HenrykRichter/A500KB/3DPrint/Checkmate_KB_Case/Case_Finished.jpeg

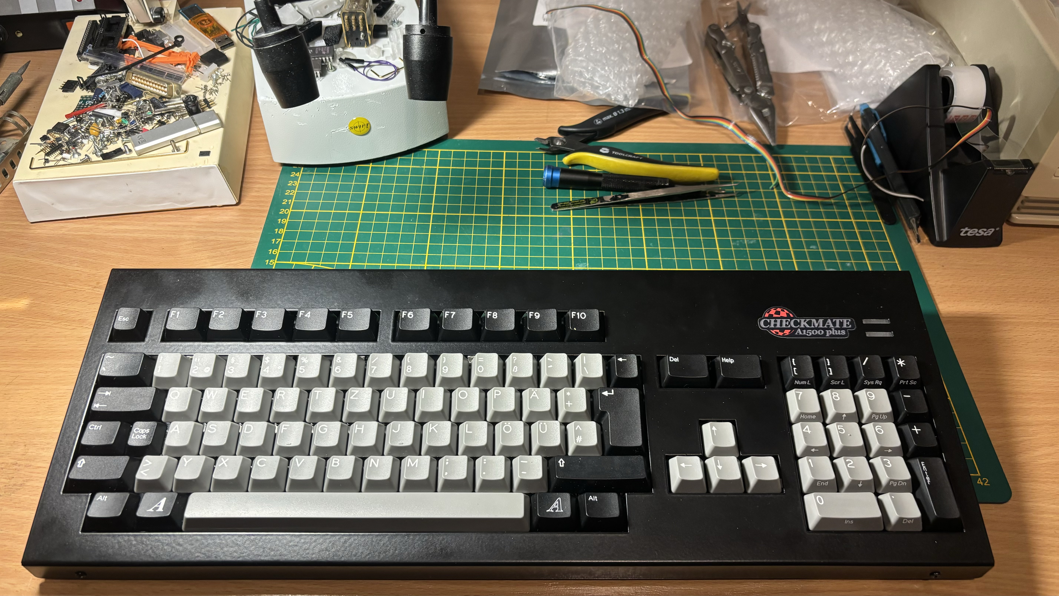
3DPrint/Checkmate_KB_Case/Case_Finished.jpeg
