HenrykRichter/A500KB/3DPrint/Checkmate_KB_Case/Case_Holders_Bottom.jpeg

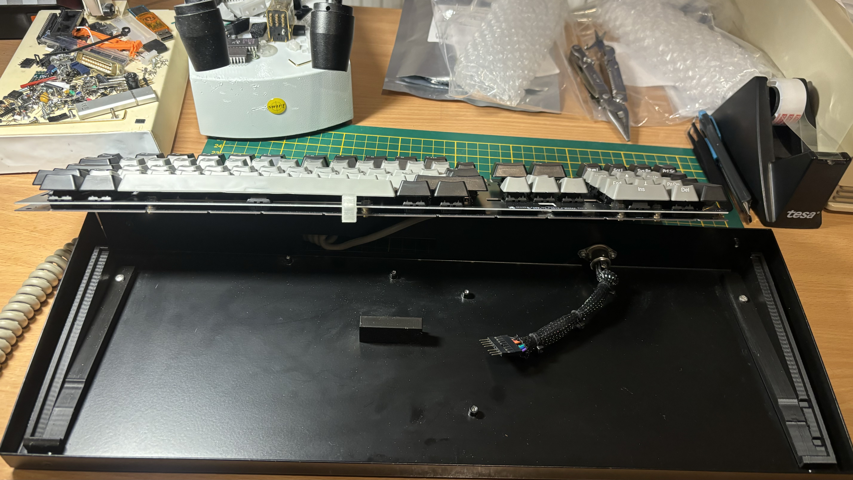
3DPrint/Checkmate_KB_Case/Case_Holders_Bottom.jpeg
