HenrykRichter/A500KB/Pics/A500KB_Config.JPG

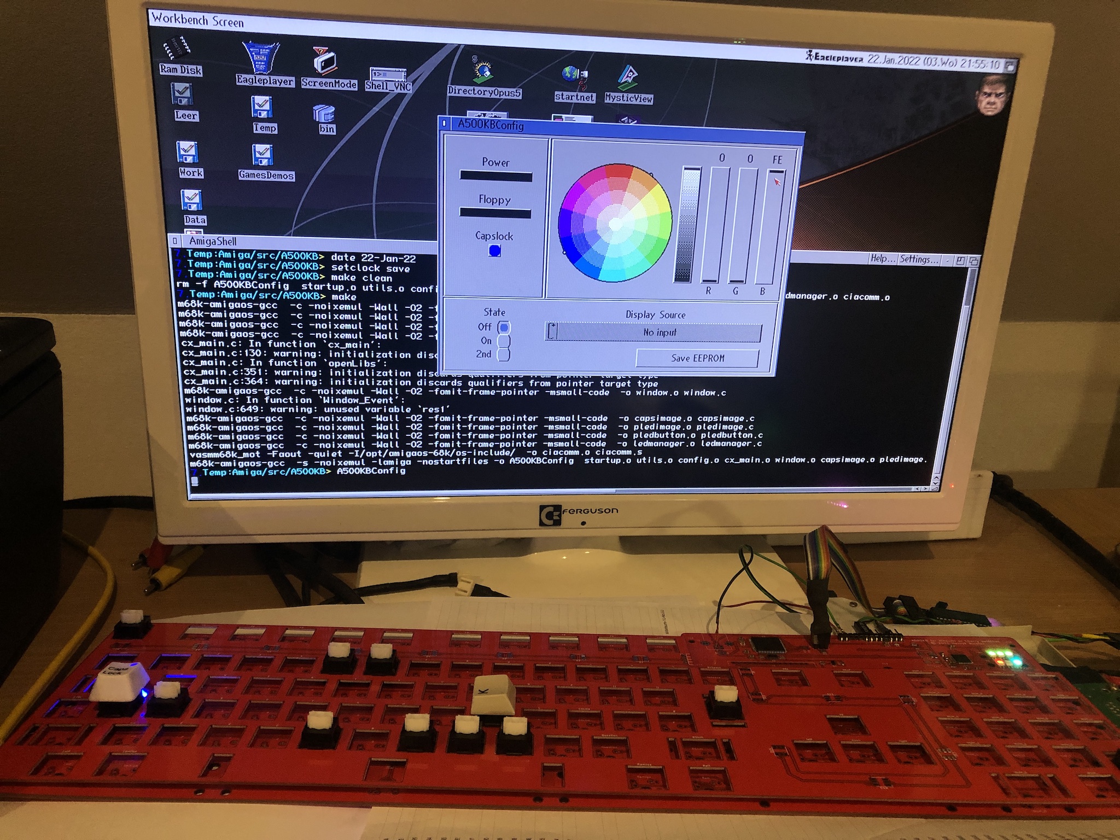
Pics/A500KB_Config.JPG
