HenrykRichter/A500KB/Pics/A500KB_LEDHolder1.JPG

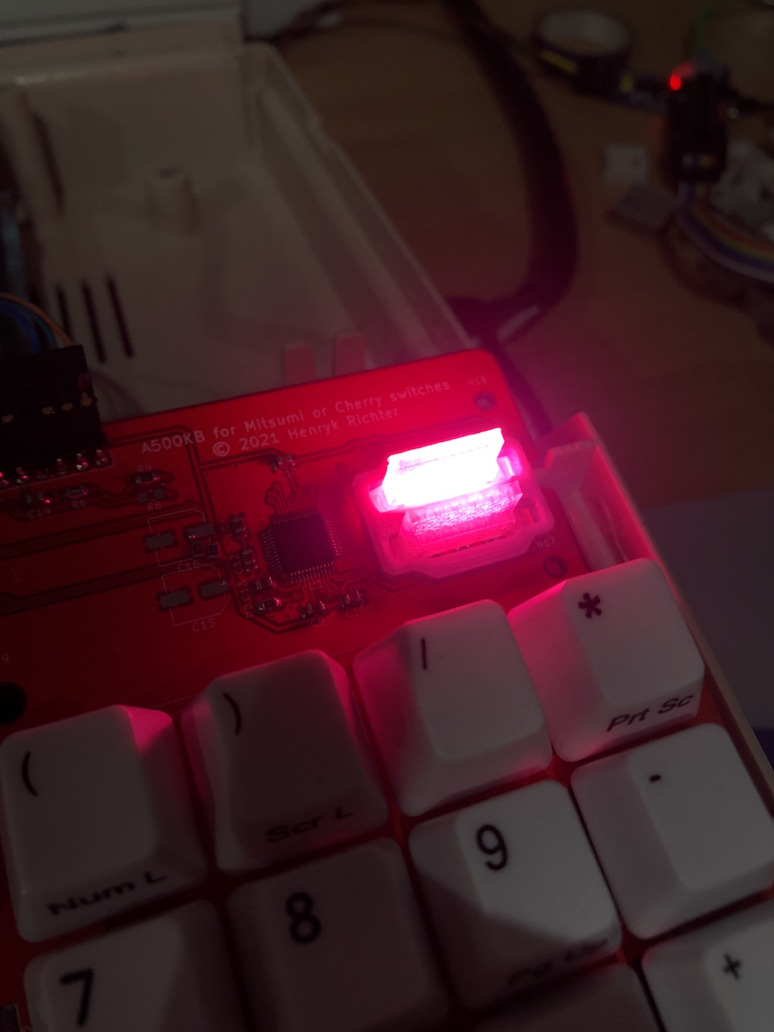
Pics/A500KB_LEDHolder1.JPG
