HenrykRichter/A500KB/Pics/A500KB_LEDHolder2.JPG

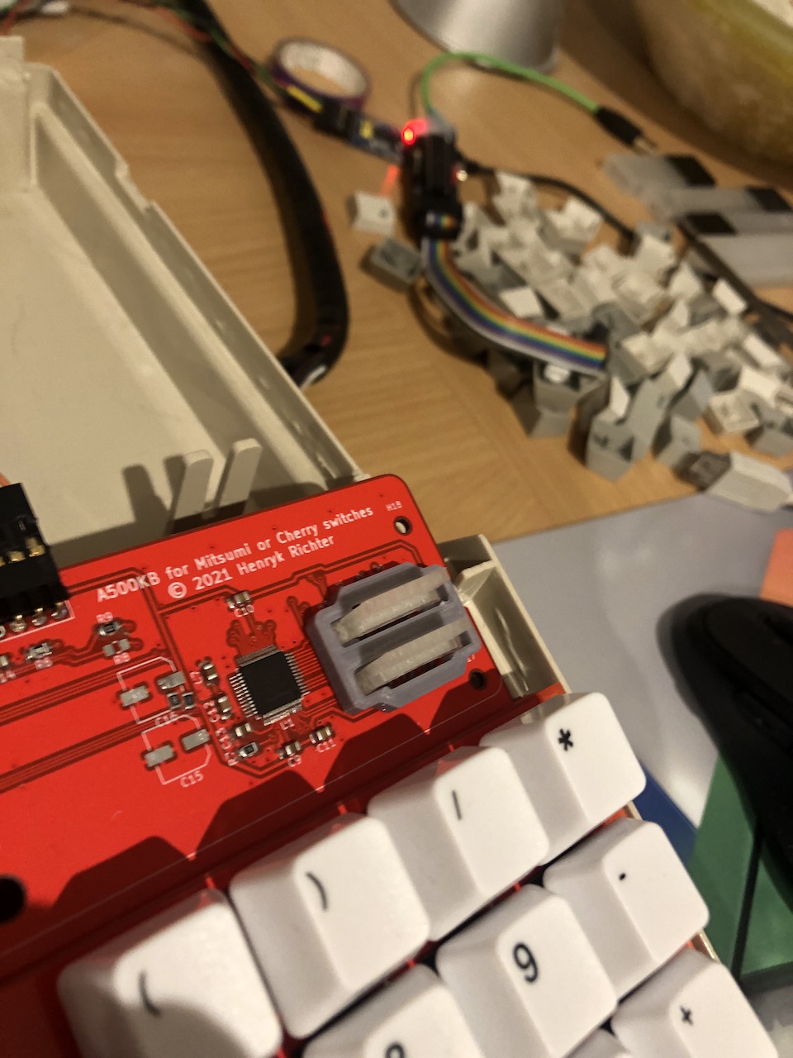
Pics/A500KB_LEDHolder2.JPG
