HenrykRichter/A500KB/Pics/A500KB_Partial.JPG

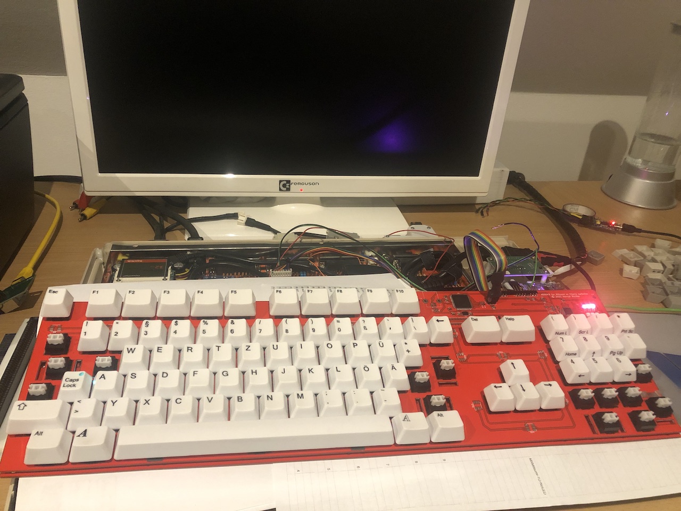
Pics/A500KB_Partial.JPG
