HenrykRichter/A500KB/Pics/A500KB_Space.JPG

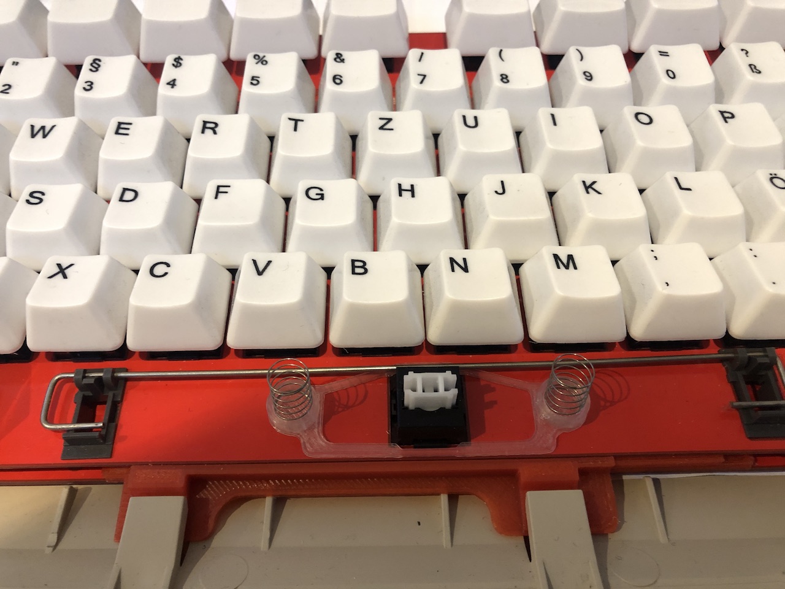
Pics/A500KB_Space.JPG
