HenrykRichter/A500KB/Pics/A500KB_Stabis.JPG

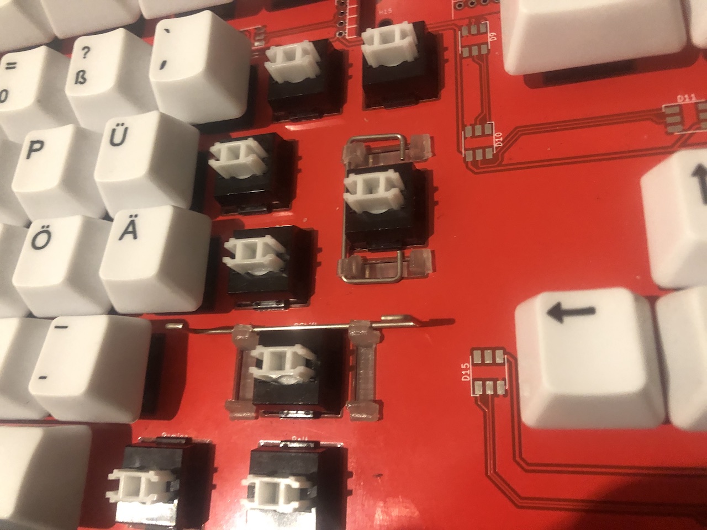
Pics/A500KB_Stabis.JPG
