HenrykRichter/A500KB/Pics/A500KB_Switches.JPG

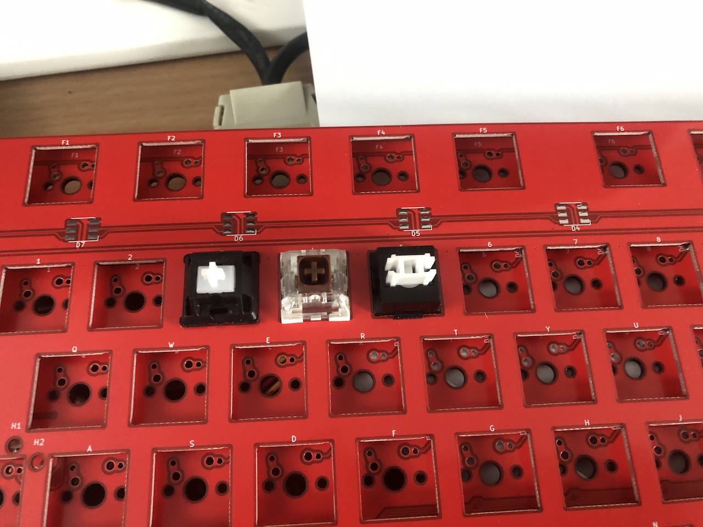
Pics/A500KB_Switches.JPG
