HenrykRichter/A500KB/Pics/A500KBMini_1.JPG

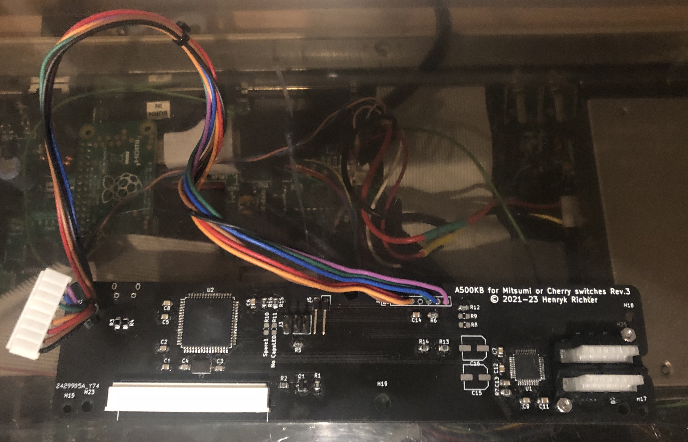
Pics/A500KBMini_1.JPG
