HenrykRichter/A500KB/Pics/A500KBMini_2.JPG

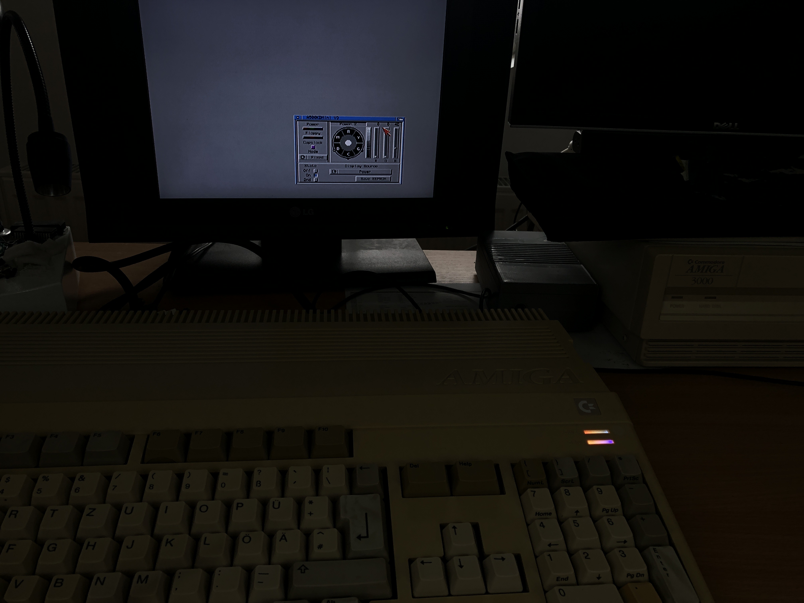
Pics/A500KBMini_2.JPG
