HenrykRichter/A500KB/Pics/A500KBMini_Freeway_Triton.JPG

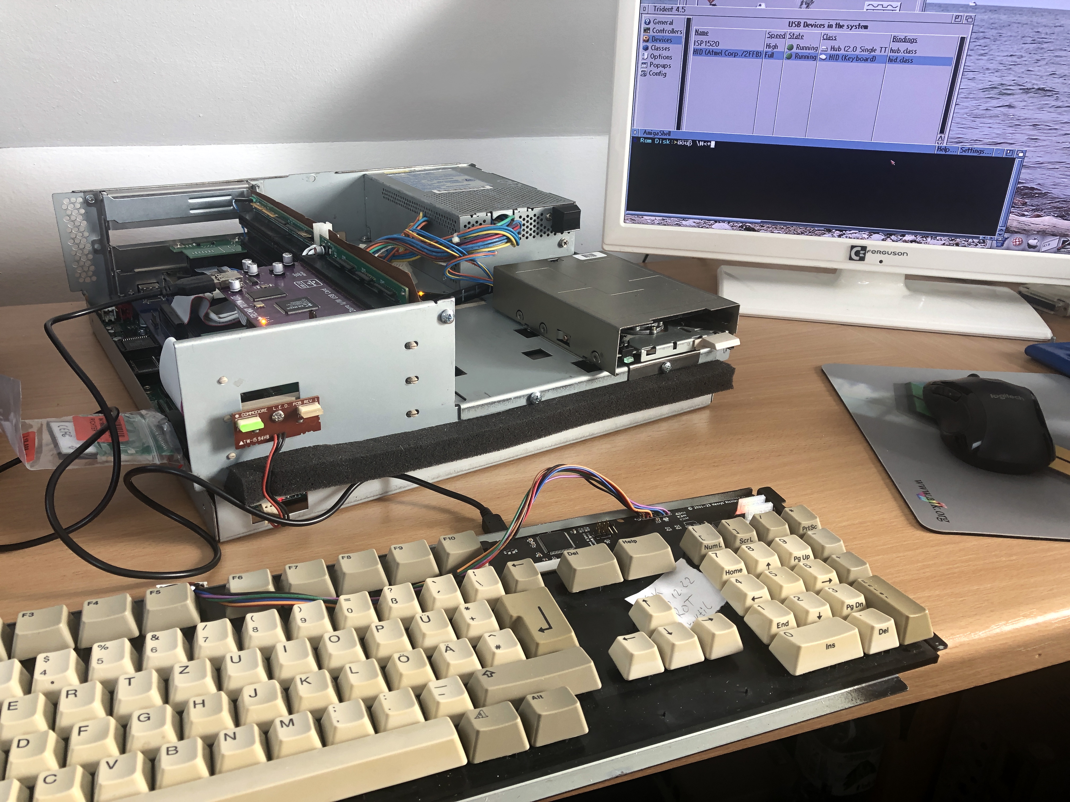
Pics/A500KBMini_Freeway_Triton.JPG
