HenrykRichter/A500KB/Pics/A500KBMini_USB_Win7.JPG

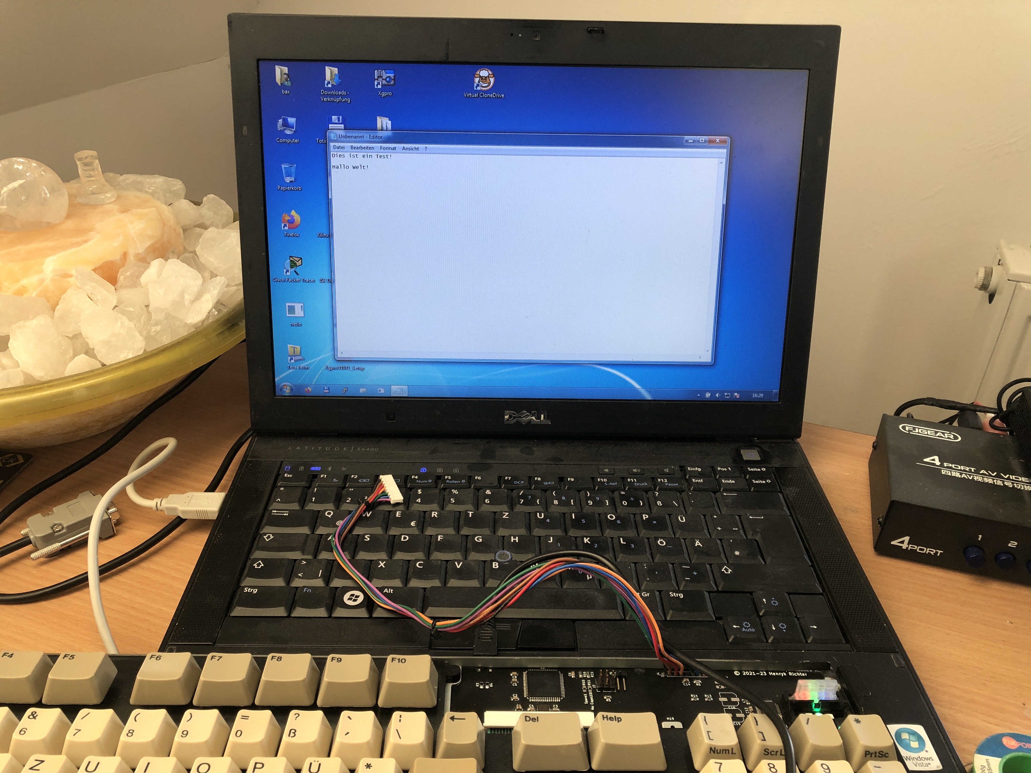
Pics/A500KBMini_USB_Win7.JPG
