HenrykRichter/A500KB/Pics/A4000_1.JPG

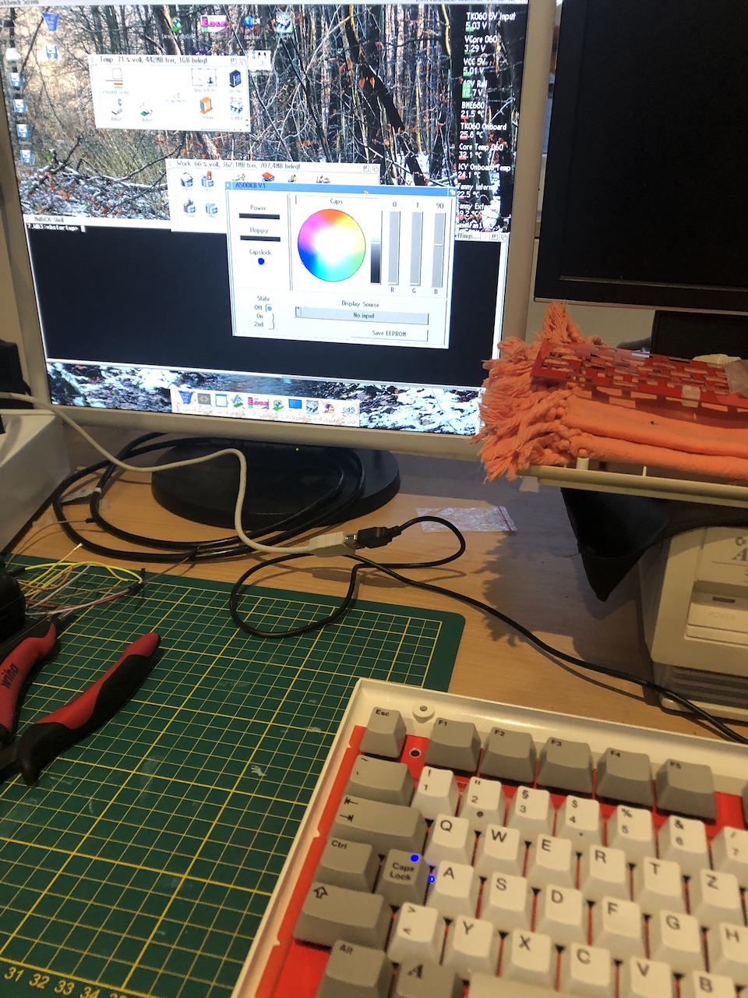
Pics/A4000_1.JPG
