HenrykRichter/A500KB/Pics/CherryKB1.JPG

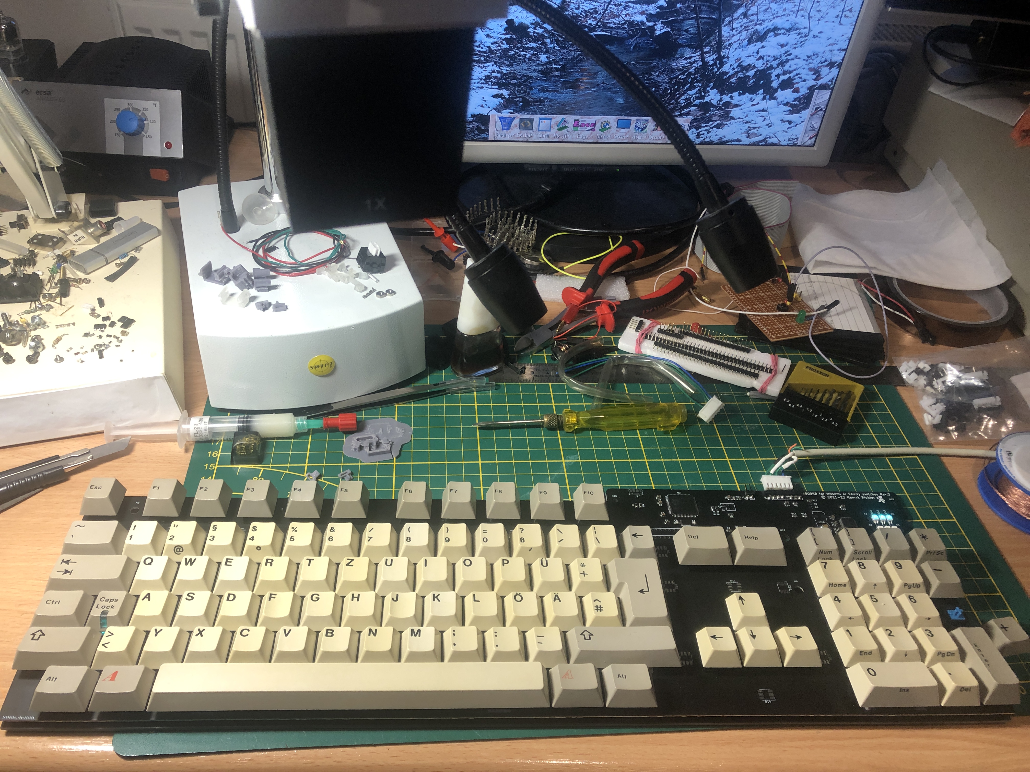
Pics/CherryKB1.JPG
