HenrykRichter/A500KB/Pics/CherryKB2.JPG

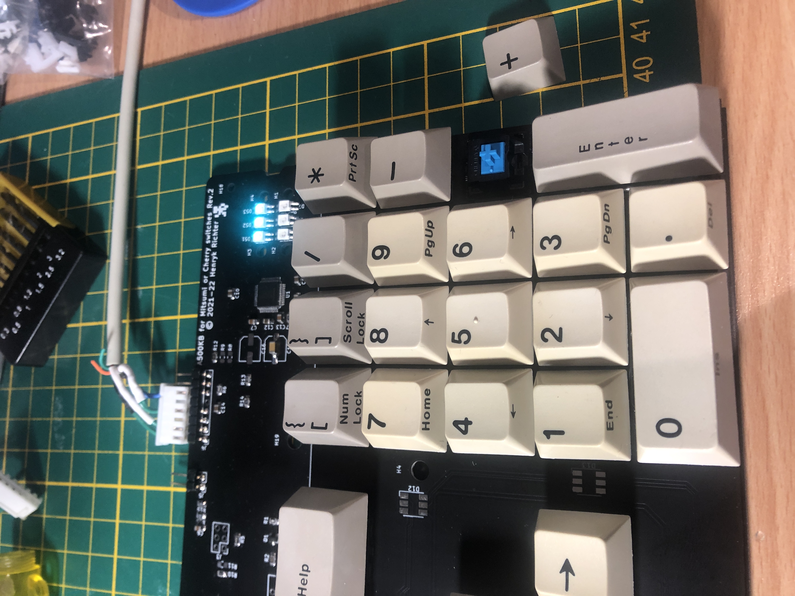
Pics/CherryKB2.JPG
