HenrykRichter/A500KB/Pics/CherryKB3.JPG

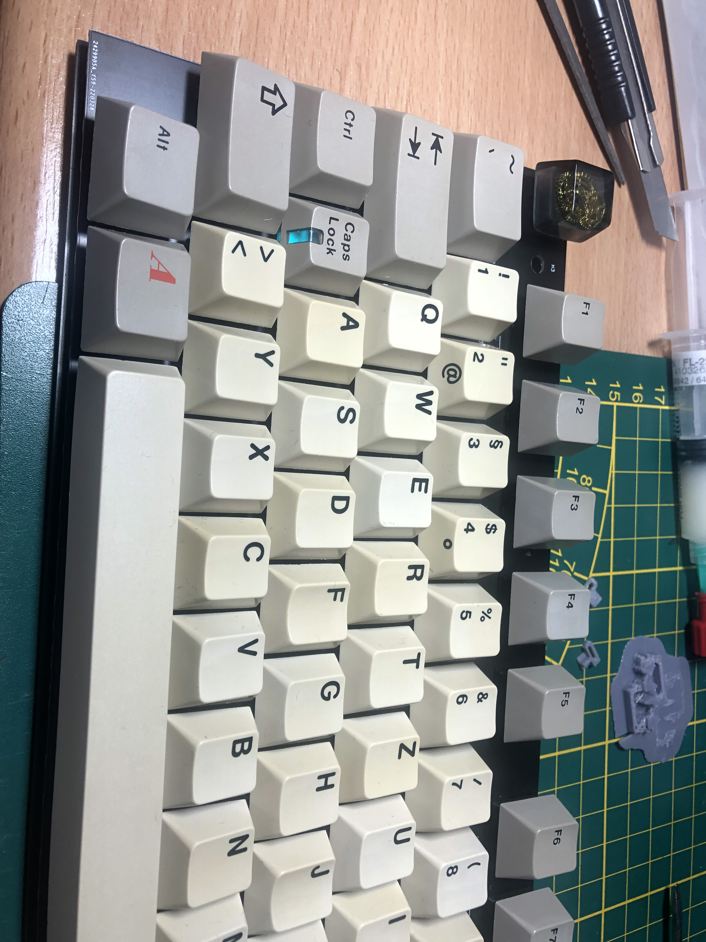
Pics/CherryKB3.JPG
