HenrykRichter/A500KB/3DPrint/Keyboard_LEDs_1.4mm_more.stl

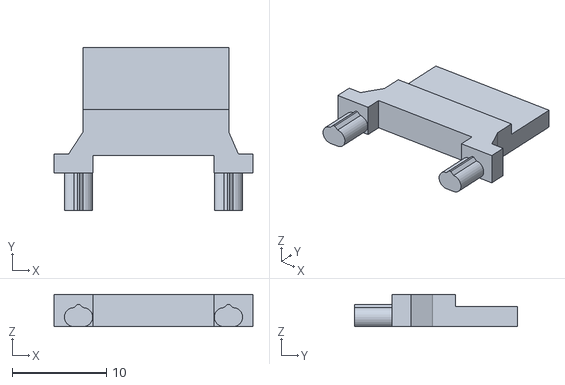
[picture p48: CAD file, 2024-06-14]
3DPrint/Keyboard_LEDs_1.4mm_more.stl
21.1 x 17.3 x 3.40
