HenrykRichter/A500KB/3DPrint/Keyboard_CapsLockLED.stl

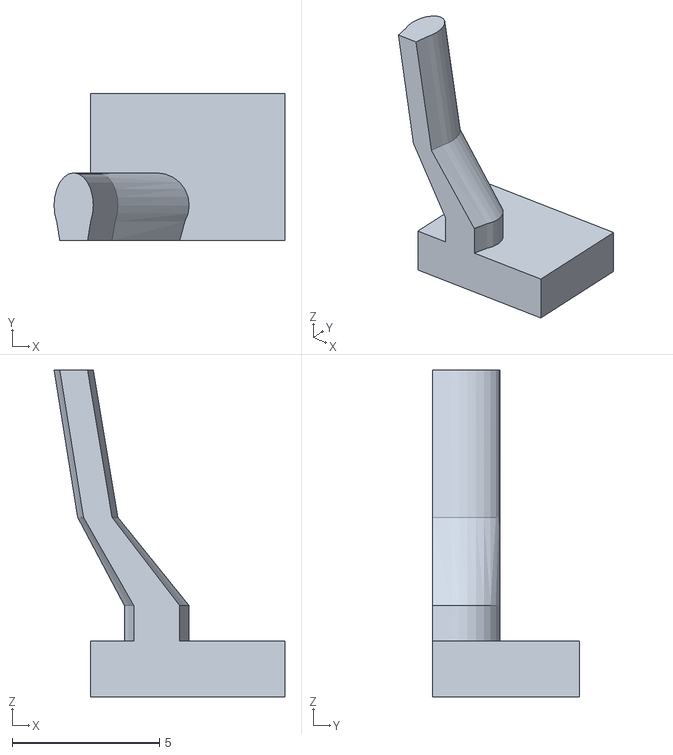
[picture p49: CAD file, 2022-02-25]
3DPrint/Keyboard_CapsLockLED.stl
7.84 x 5.00 x 11.1
