HenrykRichter/A500KB/3DPrint/Spacebar_ExtraSprings.stl

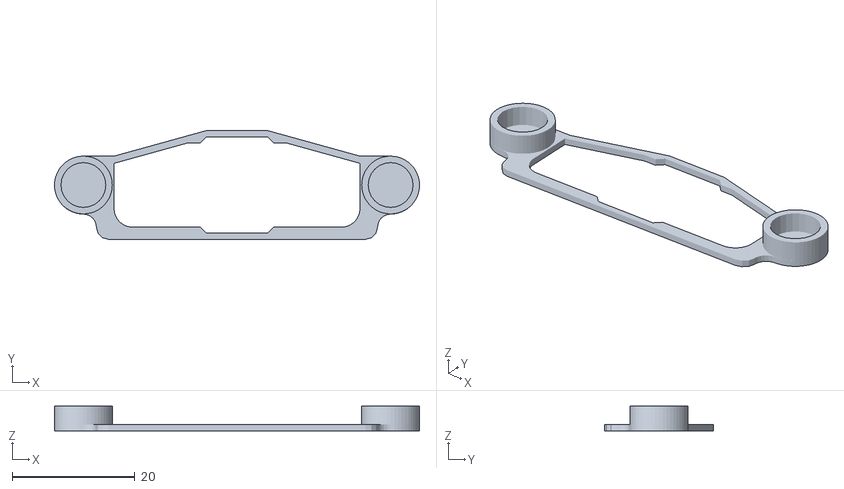
[picture p50: CAD file, 2022-01-31]
3DPrint/Spacebar_ExtraSprings.stl
59.4 x 17.7 x 4.00
