HenrykRichter/A500KB/3DPrint/Keyboard_Guide.stl

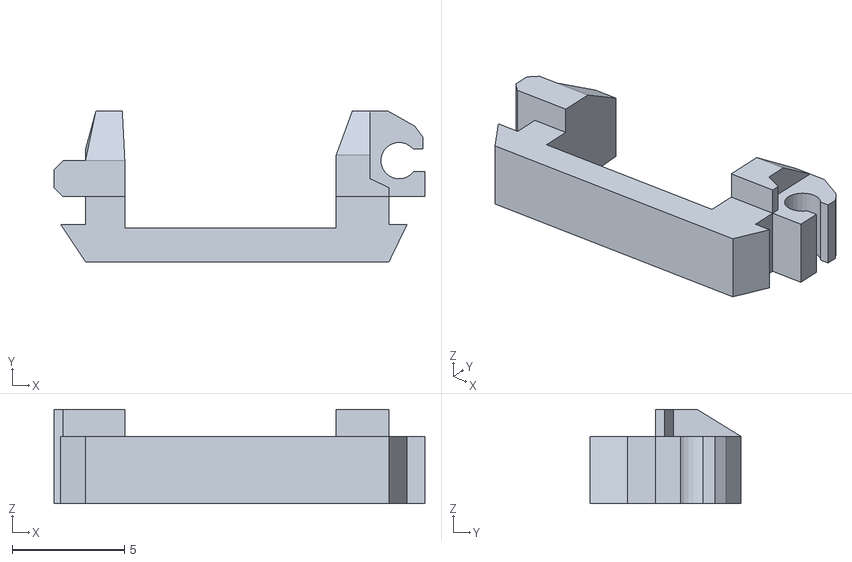
[picture p51: CAD file, 2022-01-28]
3DPrint/Keyboard_Guide.stl
16.5 x 6.70 x 4.20
