HenrykRichter/A500KB/Pics/A500KB_A500Case_potential_Problem.JPG

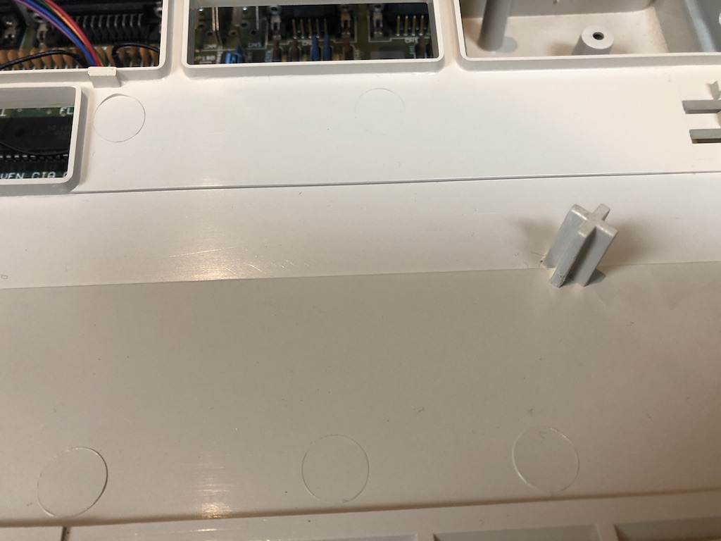
Pics/A500KB_A500Case_potential_Problem.JPG
