HenrykRichter/A500KB/src/led_digital.c

/*
 ********************************************************************************
 * led_digital.c                                                                *
 *                                                                              *
 * Author: Henryk Richter <bax@comlab.uni-rostock.de>                           *
 *                                                                              *
 * Purpose: control for digital LED strip (APA102,SK9822)                       *
 *                                                                              *
 *                                                                              *
 *                                                                              *
 *                                                                              *
 *                                                                              *
 ********************************************************************************
*/
/*
 modes:
  - static color
  - static color + moving white dot
  - rainbow slow
  - rainbow fast
  - KITT (knight rider)
  - saturation

  - splash (white in currently pressed column, then fade to static color)

*/
#define LEDD_FX_STATIC     0
#define LEDD_FX_DOT        1
#define LEDD_FX_RAINBOWSLW 2
#define LEDD_FX_RAINBOWFST 3
#define LEDD_FX_SATURATION 4
#define LEDD_FX_KITT       5

#define LEDD_FX_SPLASH     6
#define LEDD_FXMASK        0xF
#define LEDD_FXRGB         0x20

#define LEDD_STATE LED_ACTIVE

/* splash mode defines */
#define LEDD_SPLASH_IDLE  0
#define LEDD_SPLASH_INIT  1

#define LEDD_SPLASH_STEPS 50 

/* full brightness = 31 */
/* half brightness = 15 */
#define LEDD_PREAMBLE (0xE0+7)
//#define LEDD_PREAMBLE (0xE0+31)

#include <avr/interrupt.h>
#include <avr/pgmspace.h>
//#include <avr/io.h>
#include <util/delay.h> /* might be <avr/delay.h>, depending on toolchain */
//#include "avr/delay.h"
#include "baxtypes.h"
#include "spi.h"
#include "led_digital.h"
#include "led.h" /* HSV2RGB */
#define GAMMATAB_EXT
#include "gammatab.h"
#include "led_digital_splash.h"

#ifndef NULL
#define NULL (0)
#endif

#define CLIP(_a_) ((_a_) < 0) ? 0 : ( (_a_)>255 ) ? 255 : (_a_)

void LED_Start_Frame();
void LED_Stop_Frame( unsigned char nled );

unsigned char LED_update_dot( unsigned char ledd_cur, unsigned char rgbmode );
unsigned char LED_update_rainbow( unsigned char pos, unsigned char spd, unsigned char rgbmode  );
unsigned char LED_update_saturation( unsigned char pos, unsigned char spd, unsigned char rgbmode  );
unsigned char LED_update_kitt( unsigned char pos, unsigned char rgbmode );
unsigned char LED_update_splash( unsigned char ledd_cur, unsigned char rgbmode );

/* actual update rate */
#if (F_CPU == 8000000 )
#define LED_DELAY 3 
#else
#define LED_DELAY 1
#endif

unsigned char ledd_cur = 0;
unsigned char ledd_dly = LED_DELAY;
unsigned char ledd_fxstate[N_DIGI_LED]; /* private to active fx */
unsigned char ledd_fxkeycolstate[N_DIGI_LED]; /* counter for active keys per column */


void led_digital_updown(unsigned char code, unsigned char leftright)
{
	/* restrict logic to relevant mode(s) */
	if( (led_getmode( IDX_LED_DIGI ) & LEDD_FXMASK) != LEDD_FX_SPLASH )
		return;

	if( leftright >= N_DIGI_LED )
		return;

	if( code & 128 ) /* code & ( (!KEYDOWN)<<7 ) */
	{
		/* KEYUP */
		if( ledd_fxkeycolstate[leftright] > 0 )
			ledd_fxkeycolstate[leftright] -= 1;
	}
	else
	{
		/* KEYDOWN */
		ledd_fxkeycolstate[leftright] += 1;
		ledd_fxstate[leftright] = LEDD_SPLASH_INIT;
	}
}


/* call for a single time instance (~16ms) */
char led_digital_step()
{
 unsigned char fx = LEDD_FX_RAINBOWSLW; //LEDD_FX_SATURATION;//LEDD_FX_KITT; //LEDD_FX_RAINBOWSLW; //LEDD_FX_DOT;
 unsigned char rgbmode;

 fx = led_getmode( IDX_LED_DIGI );
 rgbmode = (fx & LEDD_FXRGB) ? 1 : 0;
 fx &= LEDD_FXMASK;

// { unsigned char *rgb = led_getcolor( IDX_LED_DIGI, LEDD_STATE );

#if (LED_DELAY > 0)
 /* global update interval ( 15.2ms*(1+LED_DELAY) ) */
 if( ledd_dly > 0 )
 {
 	ledd_dly--;
	return 0;
 }
 ledd_dly = LED_DELAY;
#endif

 /* start update cycle */
 LED_Start_Frame();

 /* TODO: more cute effects */
 switch( fx )
 {
	case LEDD_FX_DOT:
		ledd_cur = LED_update_dot( ledd_cur, rgbmode );break;
	case LEDD_FX_RAINBOWSLW:
		ledd_cur = LED_update_rainbow( ledd_cur, 1, rgbmode );break;
	case LEDD_FX_RAINBOWFST:
		ledd_cur = LED_update_rainbow( ledd_cur, 4, rgbmode );break;
	case LEDD_FX_SATURATION:
		ledd_cur = LED_update_saturation( ledd_cur, 1, rgbmode );break;
	case LEDD_FX_KITT:
		ledd_cur = LED_update_kitt( ledd_cur, rgbmode ); break;
	case LEDD_FX_SPLASH:
		ledd_cur = LED_update_splash( ledd_cur, rgbmode ); break;

 	case LEDD_FX_STATIC:
	default:
		ledd_cur = LED_update_dot( N_DIGI_LED, rgbmode );break;
 }

 
 LED_Stop_Frame(N_DIGI_LED);


 return 0;
}

#define N_KITT_LED 9


unsigned char LED_update_kitt( unsigned char pos, unsigned char rgbmode )
{
  unsigned char idx,r,g,b;
//  int16_t dst;
  unsigned char cur;//,dir;
//  unsigned char *rgb = led_getcolor( IDX_LED_DIGI, LEDD_STATE );

#define KITT_POSDIV 2

//  dir = 0;
  cur = ( pos>>KITT_POSDIV );
  if( cur >= N_KITT_LED )
  {
//  	dir = 1;
	if( cur >= N_KITT_LED*2 )
	{
	 cur = 0;
	 pos = 0xff;
	}
	else
	 cur = N_KITT_LED*2 - 1 - cur;
  }
  pos++;

  for( idx = 0 ; idx < N_KITT_LED ; idx++ )
  {
#define KITT_SPD 15
   if( idx == cur )
   {
   	ledd_fxstate[idx] = 255-5-(1<<KITT_POSDIV);
   }
   else
   {
    if( ledd_fxstate[idx] >= KITT_SPD )
		ledd_fxstate[idx] -= KITT_SPD; 
    else	ledd_fxstate[idx]  =  0;
   }

   r = ledd_fxstate[idx] + 5; /* some background glow */

   LCD_SPI( LEDD_PREAMBLE ); /* preamble + brightness (<31 might flicker, see https://cpldcpu.com/2014/11/30/understanding-the-apa102-superled/) */
   g = 0;
   b = 0;

   if( cur==idx )
   {
    if( (idx == 0) || (idx == (N_KITT_LED-1)))
	g = r>>5; //     g = r>>2;
   }

   if( rgbmode )
   {
    LCD_SPI( r ); // R
    LCD_SPI( b ); // B
    LCD_SPI( g ); // G
   }
   else
   {
    LCD_SPI( b ); // B
    LCD_SPI( g ); // G
    LCD_SPI( r ); // R
   }

  }

  return pos;
}


unsigned char LED_update_saturation( unsigned char pos, unsigned char spd, unsigned char rgbmode  )
{
  uint8_t rgb[3],r,g,b;
  int16_t hsv[3];
  int16_t s;
  unsigned char idx;
  unsigned char *rgb_src = led_getcolor( IDX_LED_DIGI, LEDD_STATE );

  RGB2HSV( hsv, rgb_src[0], rgb_src[1], rgb_src[2] );

  if( pos <= 127 )
  	s = 127-pos;
  else	s = pos-128; /* this hits zero twice but avoids s=128 -> s+s=256 */
  s += s; /* 0...127 -> 0..254 */

  HSV2RGB( rgb, hsv[0], s , hsv[2] );

  r = pgm_read_byte(&gamma24_tableLH[rgb[0]][GAMMATAB_H]);
  g = pgm_read_byte(&gamma24_tableLH[rgb[1]][GAMMATAB_H]);
  b = pgm_read_byte(&gamma24_tableLH[rgb[2]][GAMMATAB_H]);

  if( rgbmode )
  {
    b = pgm_read_byte(&gamma24_tableLH[rgb[0]][GAMMATAB_H]);
    g = pgm_read_byte(&gamma24_tableLH[rgb[2]][GAMMATAB_H]);
    r = pgm_read_byte(&gamma24_tableLH[rgb[1]][GAMMATAB_H]);
  }

  for( idx = 0 ; idx < N_DIGI_LED ; idx++ )
  {
	LCD_SPI( LEDD_PREAMBLE ); /* preamble + brightness */
	LCD_SPI( b );
	LCD_SPI( g ); /* BGR or BRG */
	LCD_SPI( r );
  }

  return pos+spd;
}


unsigned char LED_update_rainbow( unsigned char pos, unsigned char spd, unsigned char rgbmode  )
{
  /* pos: "H" in HSV model */
  uint16_t h = ((uint16_t)pos);
  int16_t  v;
  uint8_t rgb[3];
  unsigned char idx;
  unsigned char *rgb0 = led_getcolor( IDX_LED_DIGI, LEDD_STATE );

  /* Y0 */
  v = (int16_t)rgb0[0] + (int16_t)rgb0[1] + (int16_t)rgb0[1] + (int16_t)rgb0[2];
  v >>= 2;

  if( spd > 1 )
  {
	ledd_fxstate[0] = 0; 
	pos += spd;
  }
  else
  {
   ledd_fxstate[0] += spd;
   if( ledd_fxstate[0] > 3 )
   {
  	pos++;
	h++;
	ledd_fxstate[0] = 0;
   }
  }

//  if( spd > 1 )
	  HSV2RGB( (uint8_t*)rgb, (int16_t)( (h<<2)+ledd_fxstate[0] ), (int16_t)255, v );// (int16_t)255 );

//  h = (h<<2) + ledd_fxstate[0]; 
  for( idx = 0 ; idx < N_DIGI_LED ; idx++ )
  {
	LCD_SPI( LEDD_PREAMBLE ); /* preamble + brightness (<31 might flicker, see https://cpldcpu.com/2014/11/30/understanding-the-apa102-superled/) */
#if 1
/*	if( spd == 1 )
	{
	  if( h < 1023-4 )
	  {
	   HSV2RGB( (uint8_t*)rgb, (int16_t)( h ), (int16_t)255, v );// (int16_t)255 );
	   h = h+4;
	  }
	}
*/
	LCD_SPI( rgb[2] ); // B
	LCD_SPI( rgb[1] ); // G
	LCD_SPI( rgb[0] ); // R
#else
	LCD_SPI( pgm_read_byte( &gamma24_tableLH[rgb[2]][GAMMATAB_H] )); // B
	LCD_SPI( pgm_read_byte( &gamma24_tableLH[rgb[1]][GAMMATAB_H] )); // G
	LCD_SPI( pgm_read_byte( &gamma24_tableLH[rgb[0]][GAMMATAB_H] )); // R
#endif
  }

  return pos; /* will wrap around automatically */
}



unsigned char LED_update_dot( unsigned char ledd_cur, unsigned char rgbmode )
{
 unsigned char idx;
 unsigned char *rgb = led_getcolor( IDX_LED_DIGI, LEDD_STATE );
 unsigned char r,g,b;

 r = rgb[0];
 g = rgb[1];
 b = rgb[2];
 if( rgbmode )
 {
	b = rgb[0]; /* red */
	g = rgb[2]; /* swap r,g for RBG mode */
	r = rgb[1]; 
 }

 for( idx = 0 ; idx < N_DIGI_LED ; idx++ )
 {
  LCD_SPI( LEDD_PREAMBLE ); /* preamble + brightness (<31 might flicker, see https://cpldcpu.com/2014/11/30/understanding-the-apa102-superled/) */
  if( idx == ledd_cur )
  {
	LCD_SPI( 0xf1 ); // B
	if( rgbmode )
	{
	 LCD_SPI( 0xff ); // R
	 LCD_SPI( 0xef ); // G
	}
	else
	{
	 LCD_SPI( 0xef ); // G
	 LCD_SPI( 0xff ); // R
	}
  }
  else
  {	
	LCD_SPI( b ); // B
	LCD_SPI( g ); // G
	LCD_SPI( r ); // R
  }
 }

 /* 1 time step further */
 ledd_cur++;
 if( ledd_cur >= N_DIGI_LED )
  	ledd_cur = 0;

 return ledd_cur;
}

unsigned char LED_update_splash( unsigned char ledd_cur, unsigned char rgbmode )
{
 unsigned char idx,cnt,i,c0,c1,c2;
 unsigned char *rgb = led_getcolor( IDX_LED_DIGI, LEDD_STATE );
 int16_t ledadd[N_DIGI_LED];
 int16_t rs;

 //unsigned char ledd_fxkeycolstate[N_DIGI_LED]; /* counter for active keys per column */
 //ledd_fxstate[leftright] = LEDD_SPLASH_INIT;

 for( idx = 0 ; idx < N_DIGI_LED ; idx++ )
 {
	ledadd[idx] = 0;
 }

 /* advance time step for animation */
 for( idx = 0, cnt = 0 ; idx < N_DIGI_LED ; idx++ )
 {
  if( ledd_fxstate[idx] != LEDD_SPLASH_IDLE )
  {
   cnt++;
   ledd_fxstate[idx] += 1;

   if( ledd_fxstate[idx] >= SPLASH_ANIM_STEPS )
   {
   	ledd_fxstate[idx] = LEDD_SPLASH_IDLE;
   }
   else
   {
	const unsigned char *pos;

	i = idx;
	pos = &splash_offsets[ledd_fxstate[idx]][0];
	while( i > 0 )
	{
		i--;
		ledadd[i] += pgm_read_byte(pos++);
	}
	i = idx;
	pos = &splash_offsets[ledd_fxstate[idx]][0];
	while( i < N_DIGI_LED )
	{
		ledadd[i] += pgm_read_byte(pos++);
		i++;
	}
   }
  }
 }

 /* idle: don't waste more time */
// if( !cnt )
//	return LED_update_dot( N_DIGI_LED );

 if( rgbmode )
 {
	c0 = 0; /* RBG */
	c1 = 2;
	c2 = 1;
 }
 else
 {
	c0 = 2; /* BGR */
	c1 = 1;
	c2 = 0;
 }

 for( idx = 0 ; idx < N_DIGI_LED ; idx++ )
 {
  LCD_SPI( LEDD_PREAMBLE ); /* preamble + brightness (<31 might flicker, see https://cpldcpu.com/2014/11/30/understanding-the-apa102-superled/) */
  if( ledd_fxkeycolstate[idx] > 0 )
  {
  	/* active key column */
	LCD_SPI( 0xf1 ); // B
	LCD_SPI( 0xff ); // G
	LCD_SPI( 0xff ); // R
  }
  else
  {
	 rs = rgb[c0] + ledadd[idx];
	 LCD_SPI( CLIP(rs) ); // B
	 rs = rgb[c1] + ledadd[idx];
	 LCD_SPI( CLIP(rs) ); // G
	 rs = rgb[c2] + ledadd[idx];
	 LCD_SPI( CLIP(rs) ); // R
  }
 }

 /* 1 time step further */
 ledd_cur++;


 return ledd_cur;
}



/* reset (start frame) string to LCD row */
void LED_Start_Frame()
{
     LCD_SPI( 0 );
     LCD_SPI( 0 );
     LCD_SPI( 0 );
     LCD_SPI( 0 );
}

void LED_Stop_Frame( unsigned char nled )
{

     /* SK9822 end frame (=reset) */
     LCD_SPI( 0 );
     LCD_SPI( 0 );
     LCD_SPI( 0 );
     LCD_SPI( 0 );

     /* APA102 end frame */
     /* TODO: we should only need nled/2 zeroes */
     while( 1 )
     {
	 LCD_SPI( 0 );

	 if( nled < 8 )
	 	break;
	 nled -= 8;
     }

}
