HenrykRichter/A500KB/src/led.h

/* led controller functions */
#ifndef _INC_LED_H
#define _INC_LED_H

#include "kbdefs.h"

/* init LED controller (twi etc) */
void led_init();

/* scan inputs, return current state of all inputs (returns quickly) */
unsigned char led_getinputstate();

/* used for USB mode, explicitly set source state */
uint8_t led_setinputstate( uint8_t source, uint8_t state );

/* update controller based on input state */
unsigned char led_updatecontroller( unsigned char state );

/* save current configuration */
void led_saveconfig( char );

/* apply new configuration commands from host (command stream by serial input) 

   returns: 0 = no special action for caller
           >0 = number of bytes to send back to Amiga (typically config bytes)
	   -1 = save configuration requested
*/
char led_putcommands( unsigned char *recvcmd, unsigned char nrecv );

void HSV2RGB( uint8_t *rgb, int16_t h, int16_t s, int16_t v );
void RGB2HSV( int16_t *hsv, uint8_t r, uint8_t g, uint8_t b );


unsigned char *led_getcolor( uint8_t ledidx, uint8_t state );
unsigned char led_getmode( uint8_t ledidx );

/* force flag for led_updatecontroller() */
#define LED_FORCE_UPDATE 0x80

/* The commands are located in the upper 3 bits */
/* the lower 5 bits denote the LED index        */
#define LEDCMD_MASK   0xE0
#define LEDINDEX_MASK 0x1F
/* source change (1 byte argument) */
#define LEDCMD_SOURCE 0x20
/* color change  (4 byte argument) = state,R,G,B */
#define LEDCMD_COLOR  0x40
/* get config (1 byte argument which is currently 0) */
#define LEDCMD_GETCONFIG 0x60
/* save to EEPROM (no argument) */
#define LEDCMD_SAVECONFIG 0x80
/* get keyboard type/version */
#define LEDCMD_GETVERSION 0xA0
/* set LED mode, 1 byte argument */
#define LEDCMD_SETMODE    0xC0

/* Please note that the protocol is designed for short packets to avoid
   overflows in send/receive buffers. As a consequence, only one command
   with return values (from Keyboard to Amiga) may be issued at a time.
   This limitation concerns LEDCMD_GETVERSÌON, LEDCMD_GETCONFIG and
   LEDCMD_SAVECONFIG (asynchronous EEPROM write, where the command is
   acknowledged first and some seconds take place for the writes itself). 
   Use only one of these commands at a time.
*/

/* Arguments for GETVERSION */
#define LEDGV_HEADER     0xBA /* */
#define LEDGV_TYPE_A500  0x01 /* 7 LEDs */
#define LEDGV_TYPE_A3000 0x02 /* 1 LED only */
#define LEDGV_TYPE_A500Mini 0x03 /* 6 LEDs, no CAPS */
#define LEDGV_VERSION    0x0A /* software version (1=initial, 2=with mode support, 3=mini added, 4=USB added) */
                              /* 5=DigitalLED added, also: even numbers > 4 = no digi LED, odd numbers = digi LED
			         6=DigitalLED capable but not enabled
				 8=Watchdog added, DigitalLED capable
				 10=reverted to 16 MHz, some code optimization
			      */

/* LED MODES */
#define LEDM_STATIC  0
#define LEDM_RAINBOW 1	/* HSV rainbow */
#define LEDM_PULSE   2  /* Pulsation   */
#define LEDM_SAT     3  /* Saturation up/down */

/* LED Sources as flags used for state and change tracking */
#define LEDB_SRC_POWER  0
#define LEDB_SRC_FLOPPY 1
#define LEDB_SRC_IN3    2
#define LEDB_SRC_IN4    3
#define LEDB_SRC_CAPS   4
#define LEDF_SRC_POWER  (1<<LEDB_SRC_POWER)
#define LEDF_SRC_FLOPPY (1<<LEDB_SRC_FLOPPY)
#define LEDF_SRC_IN3    (1<<LEDB_SRC_IN3)
#define LEDF_SRC_IN4    (1<<LEDB_SRC_IN4)
#define LEDF_SRC_CAPS   (1<<LEDB_SRC_CAPS)
#define LEDF_ALL ( (LEDF_SRC_POWER)|(LEDF_SRC_FLOPPY)|(LEDF_SRC_IN3)|(LEDF_SRC_IN4)|(LEDF_SRC_CAPS) )
#define LEDB_MAP_SWAP	7
#define LEDF_MAP_SWAP	(1<<LEDB_MAP_SWAP)

#define LED_HAVE_DIGILED  !(KBD_SPARE2PIN & (1<<KBD_SPARE2B))

/* current state */
#define LED_IDLE      0 /* idle             */
#define LED_ACTIVE    1 /* primary   active */
#define LED_SECONDARY 2 /* secondary active */
#define LED_STATES    3 


/* number of LEDs */
#define N_LED         7
#define IDX_LED_DIGI  7
#define N_LED_DIGI_CONF 1 /* 1 configured color supported as of V5 */



#endif
