HenrykRichter/A500KB/src/led_digital_splash.h

#ifndef _INC_LED_DIGITAL_SPLASH_H
#define _INC_LED_DIGITAL_SPLASH_H

#if 1
/* fast moving gaussian */
#define SPLASH_ANIM_STEPS 22
const unsigned char splash_offsets[22][15] PROGMEM = {
{ 255,217,134,60,19,4,0,0,0,0,0,0,0,0,0 },/* 0 */
{ 215,239,193,113,48,14,3,0,0,0,0,0,0,0,0 },/* 1 */
{ 145,210,221,169,93,37,11,2,0,0,0,0,0,0,0 },/* 2 */
{ 78,147,203,202,146,76,29,8,1,0,0,0,0,0,0 },/* 3 */
{ 33,83,148,193,182,124,62,22,5,1,0,0,0,0,0 },/* 4 */
{ 11,37,86,147,181,161,105,49,16,4,0,0,0,0,0 },/* 5 */
{ 3,13,40,89,143,167,141,86,38,12,2,0,0,0,0 },/* 6 */
{ 0,3,14,43,90,137,151,121,70,29,9,2,0,0,0 },/* 7 */
{ 0,0,4,16,45,89,129,134,102,56,22,6,1,0,0 },/* 8 */
{ 0,0,1,5,17,46,87,118,117,84,44,16,4,0,0 },/* 9 */
{ 0,0,0,1,5,19,46,82,106,100,68,33,12,3,0 },/* 10 */
{ 0,0,0,0,1,6,19,45,76,93,83,53,25,8,2 },/* 11 */
{ 0,0,0,0,0,1,6,19,42,68,79,66,40,18,5 },/* 12 */
{ 0,0,0,0,0,0,1,6,18,38,58,64,51,29,12 },/* 13 */
{ 0,0,0,0,0,0,0,1,6,16,32,46,48,36,20 },/* 14 */
{ 0,0,0,0,0,0,0,0,1,5,13,25,34,33,23 },/* 15 */
{ 0,0,0,0,0,0,0,0,0,1,3,8,15,20,18 },/* 16 */
{ 0,0,0,0,0,0,0,0,0,0,0,1,2,4,5 },/* 17 */
{ 0,0,0,0,0,0,0,0,0,0,0,0,1,3,4 },/* 18 */
{ 0,0,0,0,0,0,0,0,0,0,0,0,0,2,3 },/* 19 */
{ 0,0,0,0,0,0,0,0,0,0,0,0,0,1,2 },/* 20 */
{ 0,0,0,0,0,0,0,0,0,0,0,0,0,0,1 }/* 21 */
};
#endif

#if 0
/* fast traveling wave */
#define SPLASH_ANIM_STEPS 23
const unsigned char splash_offsets[23][15] PROGMEM = {
{ 255,199,79,0,0,0,0,0,0,0,0,0,0,0,0 },/* 0 */
{ 204,240,171,56,0,0,0,0,0,0,0,0,0,0,0 },/* 1 */
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
{ 15,10,12,20,23,15,3,6,32,64,79,62,29,0 },/* 36 */
{ 16,10,10,17,22,17,5,3,21,53,73,65,36,9 },/* 37 */
{ 16,11,8,13,20,18,8,1,13,41,65,66,42,14 },/* 38 */
{ 16,11,8,11,17,18,10,2,7,30,56,63,46,19 },/* 39 */
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
};
#endif


#endif /* _INC_LED_DIGITAL_SPLASH_H */
