HenrykRichter/A500KB/src/gammatab.h

/*
 nonlinear RGB (8 Bit) to linear RGB (16 bit),
 based on:
  Gamma 2.4

  0.04045 toe in range (normalized range 0..1)
  12.92 toe in slope

  epsilon 0.055

*/

/* 16 bit version */
#if 0
unsigned short gamma24_table[256]={
0,19,39,59,79,99,119,139,159,
179,198,219,240,263,287,313,339,367,396,
426,458,491,525,561,598,637,676,718,761,
805,850,897,946,996,1048,1101,1156,1212,1270,
1329,1390,1453,1517,1583,1650,1719,1790,1862,1937,
2012,2090,2169,2250,2333,2417,2503,2591,2681,2772,
2866,2961,3058,3156,3257,3359,3464,3570,3678,3788,
3900,4013,4129,4246,4366,4487,4611,4736,4863,4992,
5124,5257,5392,5529,5668,5810,5953,6098,6245,6395,
6546,6700,6856,7013,7173,7335,7499,7665,7833,8004,
8176,8351,8528,8707,8888,9072,9257,9445,9635,9827,
10022,10218,10417,10618,10821,11027,11235,11445,11657,11872,
12089,12308,12530,12754,12980,13208,13439,13673,13908,14146,
14386,14629,14874,15121,15371,15623,15877,16134,16394,16655,
16920,17186,17455,17727,18000,18277,18556,18837,19121,19407,
19696,19987,20281,20577,20875,21177,21480,21787,22096,22407,
22721,23037,23356,23678,24002,24329,24658,24990,25324,25661,
26001,26343,26688,27035,27386,27738,28094,28452,28812,29176,
29542,29910,30282,30656,31032,31412,31794,32179,32566,32956,
33349,33745,34143,34544,34948,35354,35764,36176,36590,37008,
37428,37851,38277,38706,39137,39571,40008,40448,40891,41336,
41784,42235,42689,43146,43606,44068,44533,45001,45472,45946,
46423,46902,47385,47870,48358,48850,49344,49840,50340,50843,
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
{149,200},{146,202},{145,204},{148,206},{153,208},{161,210},{173,212},{187,214},{204,216},{224,218},
{247,220},{17,223},{46,225},{78,227},{113,229},{151,231},{192,233},{236,235},{27,238},{77,240},
{130,242},{186,244},{245,246},{51,249},{116,251},{184,253},{255,255} };
#endif
