HenrykRichter/A500KB/asrc/version.h

/*
  version.h

  (C) 2020 Henryk Richter <henryk.richter@gmx.net>

  version and date handling
*/
#ifndef _INC_VERSION_H
#define _INC_VERSION_H

#define PROGNAME "A500KBConfig"
#define LIBVERSION  "1"
#define LIBREVISION "9"
/* #define DEVICEEXTRA Beta */
#define LIBDATE     "28.3.25"

#endif
