HenrykRichter/A500KB/asrc/savereq.h

#ifndef _INC_SAVEREQ_H
#define _INC_SAVEREQ_H

//struct myWindow;
#include "window.h"

void SaveEEPROM_Req( struct myWindow *win );
void LoadConfig_Req( struct myWindow *win );
void About_Req( struct myWindow *win );

#endif
