HenrykRichter/A500KB/src/twi.h

#ifndef TWI_H
#define TWI_H

#include <stdint.h>

#ifndef TWI_FREQ
#define TWI_FREQ 200000UL
#endif

#ifndef TWI_BUFFER_LENGTH
#define TWI_BUFFER_LENGTH 32
#endif

void twi_init();
void twi_write(uint8_t address, uint8_t* data, uint8_t length, void (*callback)(uint8_t, uint8_t *) );
void twi_read(uint8_t address, uint8_t length, void (*callback)(uint8_t, uint8_t *));
uint8_t *twi_wait();
uint8_t twi_isbusy();

#endif
